justinalexchan/Enviro3D/images/image3.png

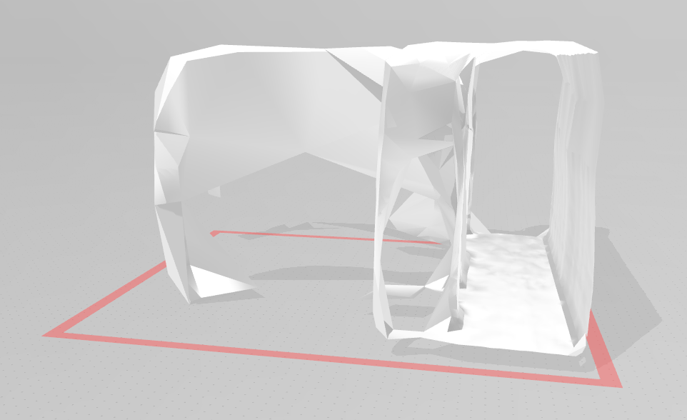
images/image3.png
