justinalexchan/Enviro3D/images/image6.png

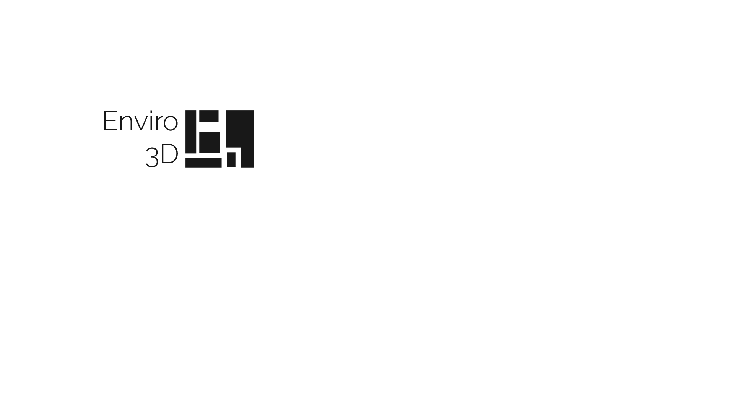
images/image6.png
