justinalexchan/Enviro3D/images/image8.png

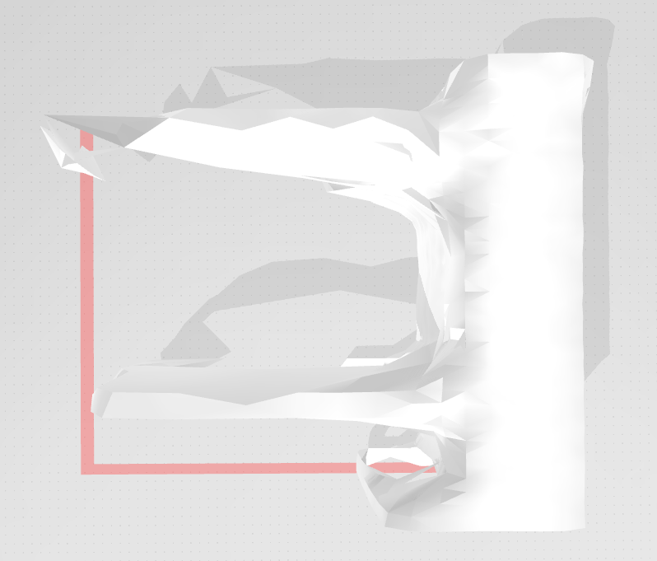
images/image8.png
